curbol/temporal/pcbs/back_plate_38/pcb.png

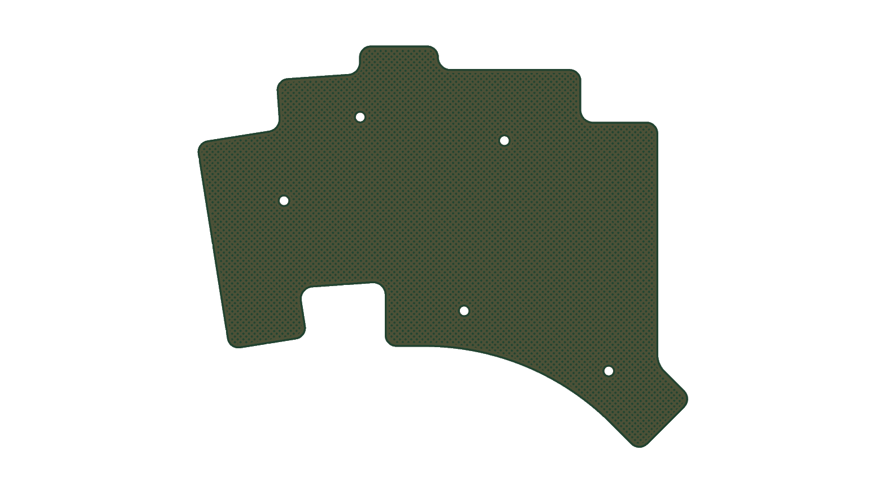
pcbs/back_plate_38/pcb.png
