curbol/temporal/pcbs/back_plate_42/pcb.png

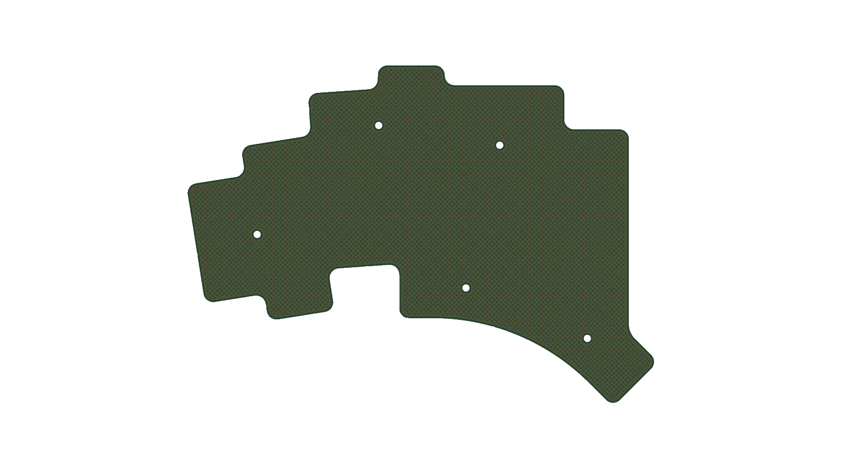
pcbs/back_plate_42/pcb.png
