curbol/temporal/pcbs/mcu_cover/pcb.png

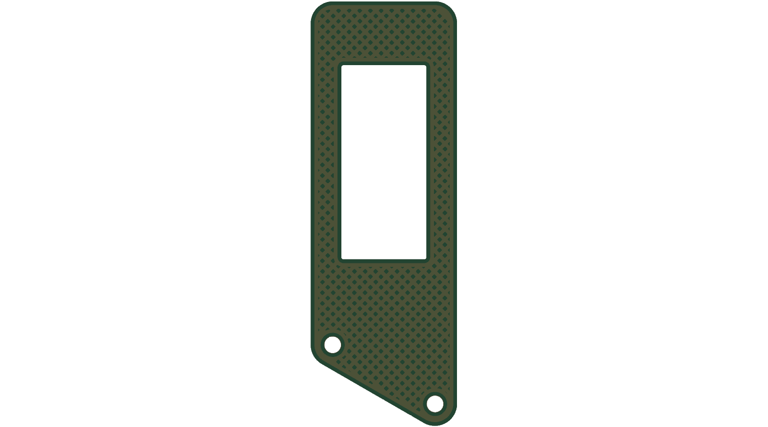
pcbs/mcu_cover/pcb.png
