curbol/temporal/pcbs/top_plate_38/pcb.png

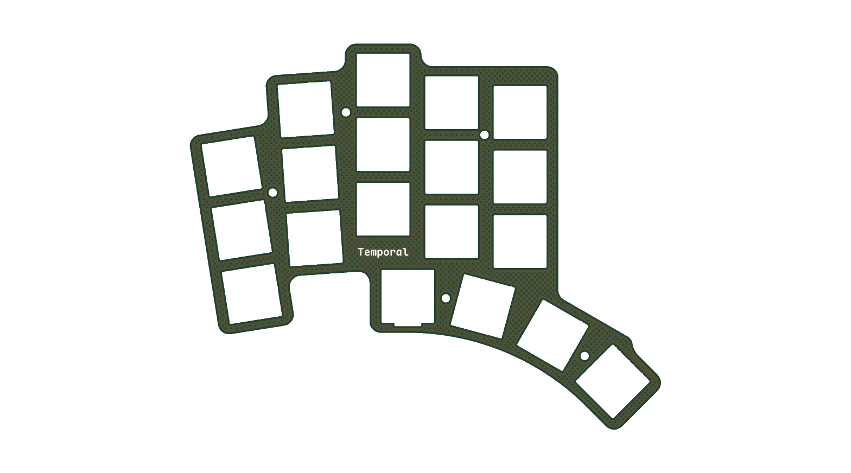
pcbs/top_plate_38/pcb.png
