curbol/temporal/pcbs/top_plate_42/pcb.png

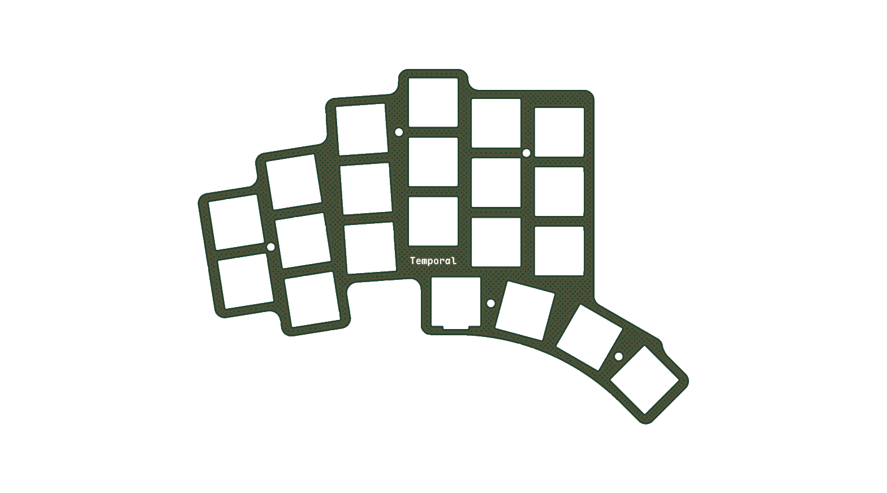
pcbs/top_plate_42/pcb.png
