curbol/temporal/assets/build_guide/display_socket_snip.jpg

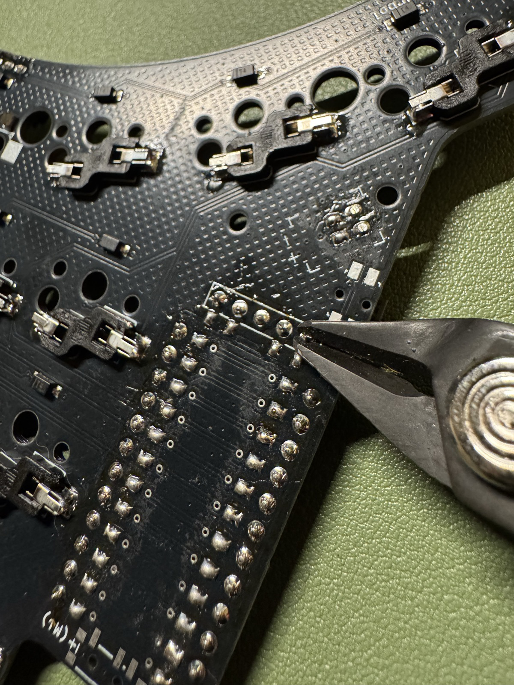
assets/build_guide/display_socket_snip.jpg
