curbol/temporal/scripts/kicad_config.yaml

# KiCad Project Defaults Configuration
# Used by scripts/setup_kicad_project.js to generate .kicad_pro files

# Default net class (applied to most signals)
# track_width, via_diameter and via_drill are not set here, and neither are the
# per-class track widths below: scripts/kicad_config.js fills them in from the
# copper_* units in ergogen/config.yaml, which size the traces and vias the
# footprints emit.
net_class_default:
  clearance: 0.2 # Clearance between traces in mm
  diff_pair_width: 0.2 # Differential pair trace width in mm
  diff_pair_gap: 0.25 # Gap between differential pair traces in mm
  microvia_diameter: 0.3 # Microvia outer diameter in mm
  microvia_drill: 0.1 # Microvia drill diameter in mm

# Additional net classes for different trace widths
net_classes:
  - name: "Power"
    clearance: 0.2
    diff_pair_width: 0.2
    diff_pair_gap: 0.25
    microvia_diameter: 0.3
    microvia_drill: 0.1

  - name: "Battery"
    clearance: 0.2
    diff_pair_width: 0.2
    diff_pair_gap: 0.25
    microvia_diameter: 0.3
    microvia_drill: 0.1

# Netclass assignment patterns (wildcards supported)
netclass_patterns:
  - pattern: "VCC"
    netclass: "Power"
  - pattern: "BAT*"
    netclass: "Battery"

# Design Rules (minimum values enforced by DRC)
design_rules:
  min_clearance: 0.0 # Minimum clearance between copper features in mm
  min_track_width: 0.0 # Minimum trace width in mm
  min_via_diameter: 0.5 # Minimum via outer diameter in mm
  min_via_annular_width: 0.1 # Minimum via annular ring width in mm
  min_copper_edge_clearance: 0.5 # Minimum clearance from board edge in mm
  min_hole_clearance: 0.25 # Minimum clearance from holes in mm
  min_hole_to_hole: 0.25 # Minimum hole-to-hole spacing in mm
  min_microvia_diameter: 0.2 # Minimum microvia outer diameter in mm
  min_microvia_drill: 0.1 # Minimum microvia drill diameter in mm
  min_through_hole_diameter: 0.3 # Minimum through-hole diameter in mm
  min_text_height: 0.8 # Minimum silkscreen text height in mm
  min_text_thickness: 0.153 # JLCPCB's minimum silkscreen stroke, 6 mil

# Custom DRC rules (written next to each board as <board>.kicad_dru)
custom_rules:
  # KiCad gives vias thermal reliefs by default. In the hatched ground pour the
  # spokes leave copper slivers and necks too narrow to fill.
  - name: "Solid zone connection for vias"
    condition: "A.Type == 'Via'"
    constraint: "zone_connection solid"

# Board Defaults
board_defaults:
  board_outline_line_width: 0.05 # Board outline line width in mm
  copper_line_width: 0.2 # Default copper line width in mm
  copper_text_size_h: 1.5 # Copper text height in mm
  copper_text_size_v: 1.5 # Copper text width in mm
  copper_text_thickness: 0.3 # Copper text thickness in mm
  # silk_line_width and silk_text_thickness come from ergogen/config.yaml's
  # silk_line_width unit, which also drives the text the footprints emit.
  silk_text_size_h: 1.0 # Silkscreen text height in mm
  silk_text_size_v: 1.0 # Silkscreen text width in mm
  zones_min_clearance: 0.5 # Minimum clearance for zones in mm

# Zone Fill Settings (used by add_ground_planes.js)
zones:
  clearance: 0.2 # Zone clearance from other features in mm
  min_thickness: 0.2 # Minimum zone fill thickness in mm
  thermal_gap: 0.254 # Thermal relief gap in mm
  thermal_bridge_width: 0.4 # Thermal relief spoke width in mm
  smoothing_radius: 0.5 # Corner smoothing radius in mm
  hatch_thickness: 0.5 # Hatch pattern line thickness in mm
  hatch_gap: 0.5 # Hatch pattern spacing in mm
  hatch_orientation: 45 # Hatch pattern orientation in degrees
  hatch_smoothing_level: 1 # Hatch smoothing (0=none, 1=light, 2=heavy)
  hatch_smoothing_value: 0.1 # Hatch smoothing strength (0-1)
  hatch_min_hole_area: 0.3 # Holes smaller than this are filled over, in mm^2
  display_hatch_pitch: 0.5 # Editor-only outline hatch pitch in mm

# Via Stitching Settings (used by via_stitching.js)
# CLI: node scripts/via_stitching.js [step_mm]
via_stitching:
  net_name: "GND" # Net name to add via stitching to
  step_mm: 6 # Spacing between vias in mm (grid size, smaller = more vias)
  # size_mm and drill_mm come from copper_via_diameter and copper_via_drill
  clearance_mm: 0.2 # Clearance around vias in mm

# Text Keepout Settings (used by create_text_keepouts.js)
text_keepouts:
  gap_mm: 0 # Inflation around the text outline in mm (0 follows the glyphs exactly)
  patterns: ["Temporal", "curbol", "Right", "Left", "Back", "(M↓)"] # Text to create keepouts for (empty array = all text)

# JLCPCB Assembly Configuration (used by generate_jlcpcb_files.js)
jlcpcb:
  assembly_parts:
    - footprint: "ceoloide:diode_tht_sod123"
      lcsc_part: "C81598"
      description: "1N4148W Diode SOD-123"

  # Embedded resistor pads within parent footprints (for jumper bridging)
  # These are 0402 0-ohm resistors that overlay solder jumper pads
  embedded_resistors:
    lcsc_part: "C17168"  # 0402 0-ohm resistor
    description: "0402 0-Ohm Resistor"

    # MCU resistor positions (relative to footprint center)
    # 12 rows per side, 2 resistors per row (left and right)
    mcu_nice_nano:
      parent_footprint: "ceoloide:mcu_nice_nano"
      resistor_x_offsets: [-5.03, 5.03]  # Center between pad pairs
      resistor_y_offsets: [-12.7, -10.16, -7.62, -5.08, -2.54, 0, 2.54, 5.08, 7.62, 10.16, 12.7, 15.24]
      rotation_offset: 0  # Horizontal pads need 0° rotation

    # Display resistor positions (relative to footprint center)
    # 4 resistors for CS, SCK, MOSI, VCC signals
    display_nice_view:
      parent_footprint: "ceoloide:display_nice_view"
      positions:  # [x, y] relative to footprint
        - [-5.08, 14.5]
        - [-2.54, 14.5]
        - [2.54, 14.5]
        - [5.08, 14.5]
      rotation_offset: 90

    # Battery resistor positions (relative to footprint center)
    # 2 resistors for BAT_P and BAT_N
    battery_connector:
      parent_footprint: "ceoloide:battery_connector_jst_ph_2"
      positions:
        - [-1, 2.158]  # BAT_P side
        - [1, 2.158]   # BAT_N side
      rotation_offset: 90  # Vertical pads need 90° rotation
